ElKinoflop/Barghest/images/PXL_20241010_131253311.jpg

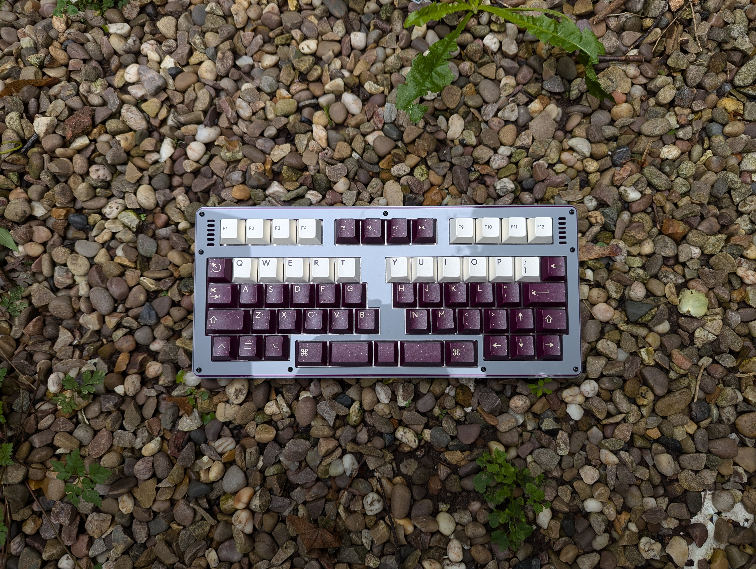
images/PXL_20241010_131253311.jpg
